capitaoananas/40ish-splitkeyboard-v2/Reders/40%ish_v2_case_2025-Jul-05_04-43-53PM-000_CustomizedView12102083412.png

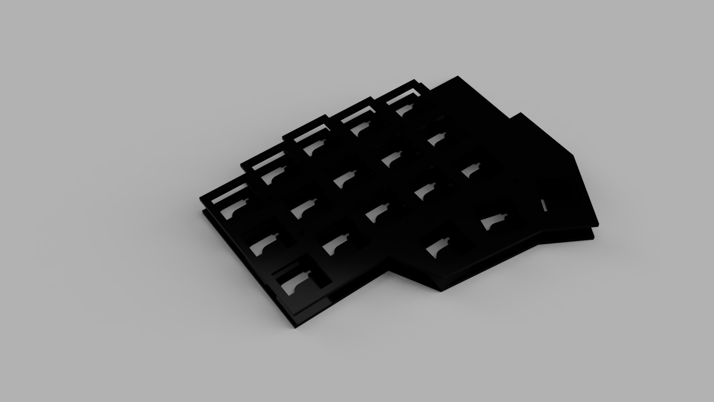
Reders/40%ish_v2_case_2025-Jul-05_04-43-53PM-000_CustomizedView12102083412.png
