capitaoananas/40ish-splitkeyboard-v2/Reders/40%ish_v2_case_2025-Jul-05_04-47-33PM-000_CustomizedView64372193932.png

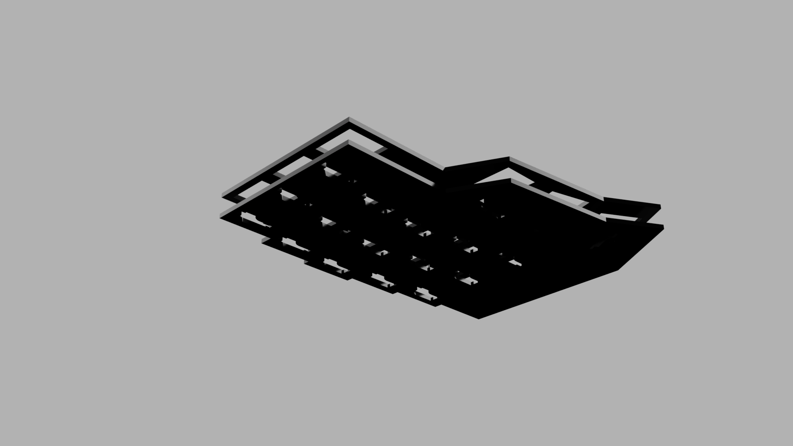
Reders/40%ish_v2_case_2025-Jul-05_04-47-33PM-000_CustomizedView64372193932.png
