capitaoananas/40ish-splitkeyboard-v2/Reders/40%ish_v2_case_2025-Jul-05_04-47-52PM-000_CustomizedView7167316527.png

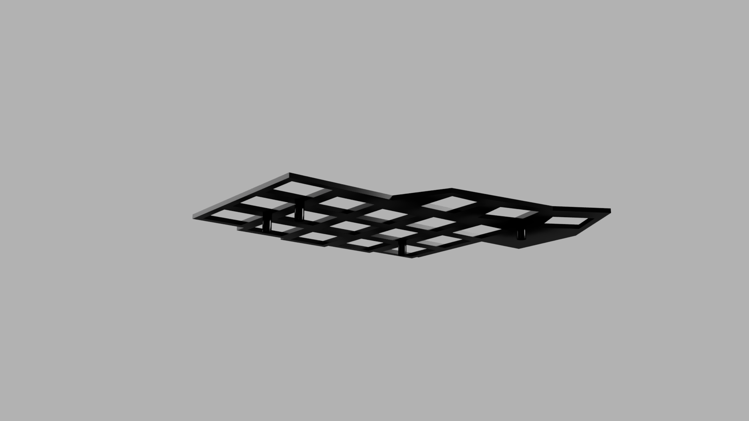
Reders/40%ish_v2_case_2025-Jul-05_04-47-52PM-000_CustomizedView7167316527.png
