capitaoananas/40ish-splitkeyboard-v2/Reders/40%ish_v2_case_2025-Jul-05_04-50-41PM-000_CustomizedView27644930984.png

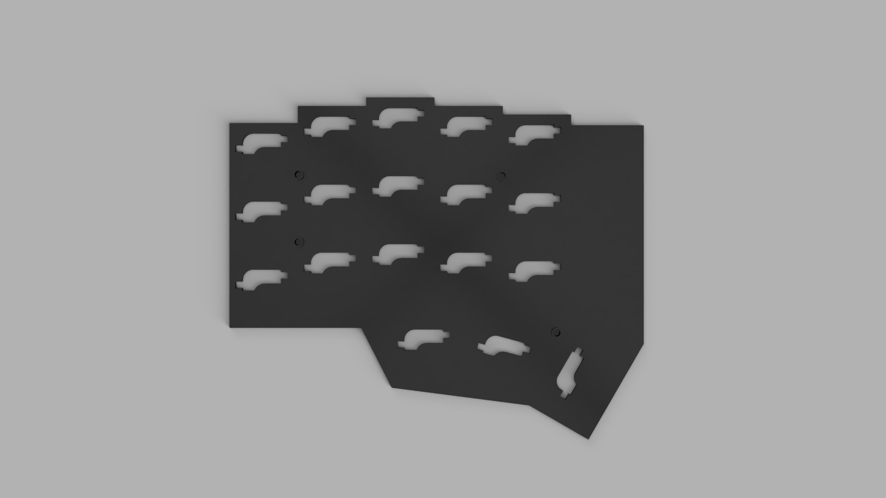
Reders/40%ish_v2_case_2025-Jul-05_04-50-41PM-000_CustomizedView27644930984.png
